thor2643/P2-Demo-Robot-Cell/Code/TCPServer/GUI_Server/resources/black_black.png

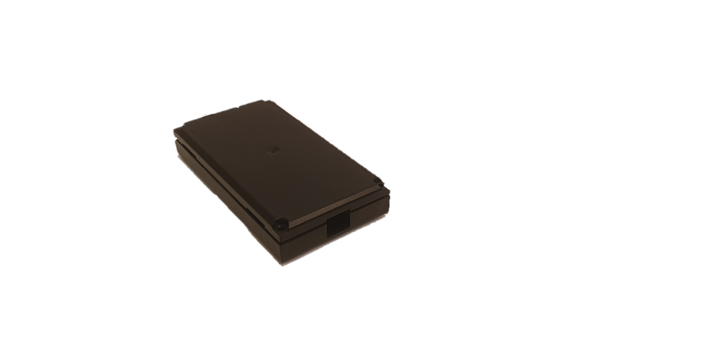
Code/TCPServer/GUI_Server/resources/black_black.png
