thor2643/P2-Demo-Robot-Cell/Code/TCPServer/GUI_Server/include/app.hpp

// Dear ImGui: standalone example application for GLFW + OpenGL2, using legacy fixed pipeline
// (GLFW is a cross-platform general purpose library for handling windows, inputs, OpenGL/Vulkan/Metal graphics context creation, etc.)

// Learn about Dear ImGui:
// - FAQ                  https://dearimgui.com/faq
// - Getting Started      https://dearimgui.com/getting-started
// - Documentation        https://dearimgui.com/docs (same as your local docs/ folder).
// - Introduction, links and more at the top of imgui.cpp

// **DO NOT USE THIS CODE IF YOUR CODE/ENGINE IS USING MODERN OPENGL (SHADERS, VBO, VAO, etc.)**
// **Prefer using the code in the example_glfw_opengl2/ folder**
// See imgui_impl_glfw.cpp for details.

#include "imgui.h"
#include "imgui_impl_glfw.h"
#include "imgui_impl_opengl2.h"
#include <stdio.h>
#include <iostream>
#ifdef __APPLE__
#define GL_SILENCE_DEPRECATION
#endif
#include <GLFW/glfw3.h>

// [Win32] Our example includes a copy of glfw3.lib pre-compiled with VS2010 to maximize ease of testing and compatibility with old VS compilers.
// To link with VS2010-era libraries, VS2015+ requires linking with legacy_stdio_definitions.lib, which we do using this pragma.
// Your own project should not be affected, as you are likely to link with a newer binary of GLFW that is adequate for your version of Visual Studio.
#if defined(_MSC_VER) && (_MSC_VER >= 1900) && !defined(IMGUI_DISABLE_WIN32_FUNCTIONS)
#pragma comment(lib, "legacy_stdio_definitions")
#endif

static void glfw_error_callback(int error, const char* description)
{
    fprintf(stderr, "GLFW Error %d: %s\n", error, description);
}


/*
This class helps making the main code cleaner by implementing all the obligatory
stuff to run imgui with glfw and opengl2. The code has been directly copied from the
main.cpp in example_glfw_opengl2 folder from the imgui github.
The update function will be overridden in another class, where custom GUI stuff
is coded.
*/ 
class App {
    public:
        App(int width, int height) {
            glfwSetErrorCallback(glfw_error_callback);
            if (!glfwInit())
                std::exit(1);

            // Create window with graphics context
            window = glfwCreateWindow(width, height, "P2 Robot Cell Demonstration", nullptr, nullptr);
            if (window == nullptr)
                std::exit(1);

            glfwMakeContextCurrent(window);
            glfwSwapInterval(1); // Enable vsync

            // Setup Dear ImGui context
            IMGUI_CHECKVERSION();
            ImGui::CreateContext();
            ImGuiIO& io = ImGui::GetIO(); (void)io;
            io.ConfigFlags |= ImGuiConfigFlags_NavEnableKeyboard;     // Enable Keyboard Controls
            io.ConfigFlags |= ImGuiConfigFlags_NavEnableGamepad;      // Enable Gamepad Controls
            io.Fonts->AddFontFromFileTTF("../libs/imgui/misc/fonts/Roboto-Medium.ttf", 20);

            // Setup Dear ImGui style
            ImGui::StyleColorsDark();
            //ImGui::StyleColorsLight();

            // Setup Platform/Renderer backends
            ImGui_ImplGlfw_InitForOpenGL(window, true);
            ImGui_ImplOpenGL2_Init();

            // Load Fonts
            // - If no fonts are loaded, dear imgui will use the default font. You can also load multiple fonts and use ImGui::PushFont()/PopFont() to select them.
            // - AddFontFromFileTTF() will return the ImFont* so you can store it if you need to select the font among multiple.
            // - If the file cannot be loaded, the function will return a nullptr. Please handle those errors in your application (e.g. use an assertion, or display an error and quit).
            // - The fonts will be rasterized at a given size (w/ oversampling) and stored into a texture when calling ImFontAtlas::Build()/GetTexDataAsXXXX(), which ImGui_ImplXXXX_NewFrame below will call.
            // - Use '#define IMGUI_ENABLE_FREETYPE' in your imconfig file to use Freetype for higher quality font rendering.
            // - Read 'docs/FONTS.md' for more instructions and details.
            // - Remember that in C/C++ if you want to include a backslash \ in a string literal you need to write a double backslash \\ !
            //io.Fonts->AddFontDefault();
            //io.Fonts->AddFontFromFileTTF("c:\\Windows\\Fonts\\segoeui.ttf", 18.0f);
            //io.Fonts->AddFontFromFileTTF("../../misc/fonts/DroidSans.ttf", 16.0f);
            //io.Fonts->AddFontFromFileTTF("../../misc/fonts/Roboto-Medium.ttf", 16.0f);
            //io.Fonts->AddFontFromFileTTF("../../misc/fonts/Cousine-Regular.ttf", 15.0f);
            //ImFont* font = io.Fonts->AddFontFromFileTTF("c:\\Windows\\Fonts\\ArialUni.ttf", 18.0f, nullptr, io.Fonts->GetGlyphRangesJapanese());
            //IM_ASSERT(font != nullptr);

        }

        virtual ~App(){
            // Cleanup
            ImGui_ImplOpenGL2_Shutdown();
            ImGui_ImplGlfw_Shutdown();
            ImGui::DestroyContext();

            glfwDestroyWindow(window);
            glfwTerminate();

        }

        void Run(){
            StartUp();

            while (!glfwWindowShouldClose(window)){
                glfwPollEvents();

                // Start the Dear ImGui frame
                ImGui_ImplOpenGL2_NewFrame();
                ImGui_ImplGlfw_NewFrame();
                ImGui::NewFrame();

                Update();

                // Rendering
                ImGui::Render();
                int display_w, display_h;
                glfwGetFramebufferSize(window, &display_w, &display_h);
                glViewport(0, 0, display_w, display_h);
                glClearColor(clear_color.x * clear_color.w, clear_color.y * clear_color.w, clear_color.z * clear_color.w, clear_color.w);
                glClear(GL_COLOR_BUFFER_BIT);

                // If you are using this code with non-legacy OpenGL header/contexts (which you should not, prefer using imgui_impl_opengl3.cpp!!),
                // you may need to backup/reset/restore other state, e.g. for current shader using the commented lines below.
                //GLint last_program;
                //glGetIntegerv(GL_CURRENT_PROGRAM, &last_program);
                //glUseProgram(0);
                ImGui_ImplOpenGL2_RenderDrawData(ImGui::GetDrawData());
                //glUseProgram(last_program);

                glfwMakeContextCurrent(window);
                glfwSwapBuffers(window);
            }
        }

        virtual void Update() = 0;
        virtual void StartUp() = 0;

        ImVec4 clear_color = ImVec4(0.45f, 0.55f, 0.60f, 1.00f);
         

    private:
        GLFWwindow* window;
        
};
