thor2643/P2-Demo-Robot-Cell/Code/TCPServer/GUI_Server/include/URSocket.hpp

#ifndef TCP_SOCKET_HPP
#define TCP_SOCKET_HPP

#ifdef _WIN32
  /* See http://stackoverflow.com/questions/12765743/getaddrinfo-on-win32 */
  #define NTDDI_VERSION NTDDI_VISTA 
  //#define _WIN32_WINNT _WIN32_WINNT_VISTA 

  #include <winsock2.h>
  #include <Ws2tcpip.h>

#else
  /* Assume that any non-Windows platform uses POSIX-style sockets instead. */
  #include <sys/socket.h>
  #include <arpa/inet.h>
  #include <netdb.h>  /* Needed for getaddrinfo() and freeaddrinfo() */
  #include <unistd.h> /* Needed for close() */
  #include <fcntl.h>
  #include <errno.h>
  
  typedef int SOCKET;
  #define INVALID_SOCKET -1
  #define SOCKET_ERROR -1
  #define WSAEWOULDBLOCK EWOULDBLOCK 
  #define WSAENOTSOCK ENOTSOCK
  #define WSAECONNRESET ECONNRESET
  #define WSAEISCONN EISCONN
  #define WSAEALREADY EALREADY
  #define WSAEINVAL EINPROGRESS

#endif

#include <cstring>

class URSocket {
    public:
        URSocket(int port);
        ~URSocket();

        int SockInit(int port);
        int SockQuit(void);
        int SockClose(SOCKET sock);

        bool Connected();
        bool AcceptConnection();
        bool HandleConnection(char* msg);
        bool Send(char* msg, int msg_type = 1);
        void Disconnect();


    private:
      bool _connected;

      SOCKET _socket;
      SOCKET _server_socket;

};

class RoboDKClient {
    public:
        RoboDKClient();
        ~RoboDKClient();

        int SockInit();
        int SockQuit();
        int SockClose(SOCKET sock);

        bool Connected();
        bool Connect(const char* host, int port);
        bool HandleConnection(char* msg);
        void Send(char* msg);
        void Disconnect();


    private:
      bool _connected;

      SOCKET _socket;

};


#endif 
